nic6911/ESP32_Modbus_Module/esphome_example_code/Heatpump_lovelace_card/heatpump.png

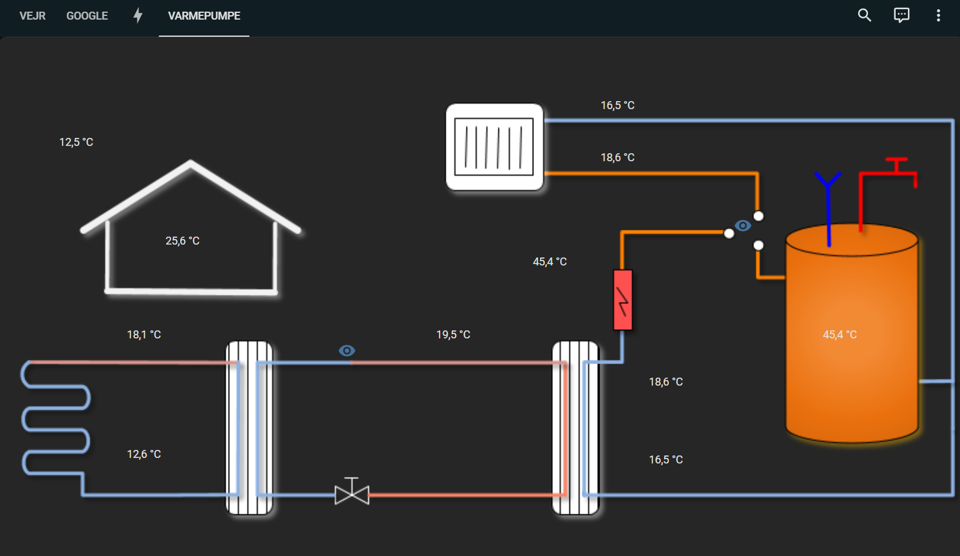
esphome_example_code/Heatpump_lovelace_card/heatpump.png
