nic6911/ESP32_Modbus_Module/esphome_example_code/Nilan_lovelace_card/CTS400/example.png

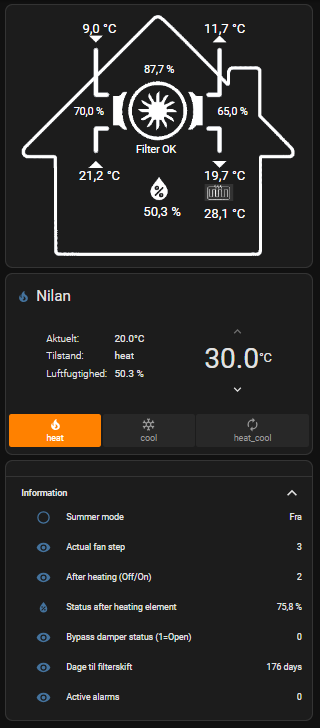
esphome_example_code/Nilan_lovelace_card/CTS400/example.png
