nic6911/ESP32_Modbus_Module/esphome_example_code/Nilan_lovelace_card/ventilation_light.png

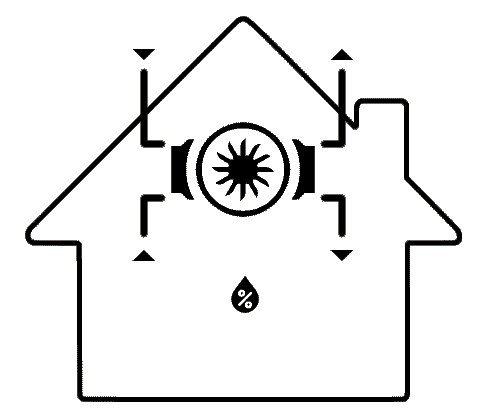
esphome_example_code/Nilan_lovelace_card/ventilation_light.png
